fablabnk/SynthLabBadge/BuildGuide/ComponentImages/1.1k-ohm.png

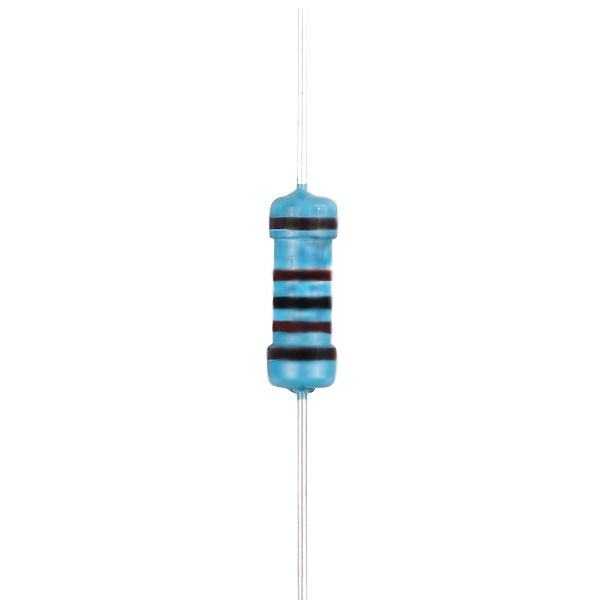
BuildGuide/ComponentImages/1.1k-ohm.png
