fablabnk/SynthLabBadge/BuildGuide/ComponentImages/1N4007.jpeg

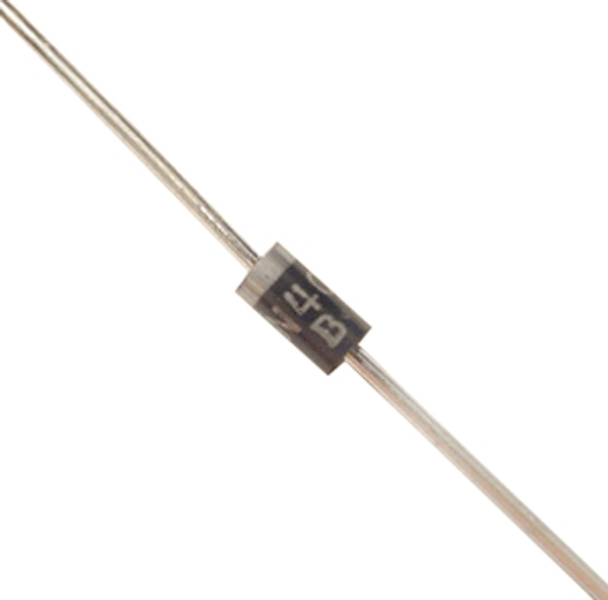
BuildGuide/ComponentImages/1N4007.jpeg
