fablabnk/SynthLabBadge/BuildGuide/ComponentImages/61201021621_sml.webp

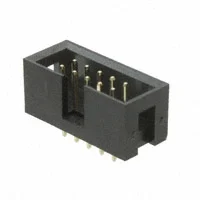
BuildGuide/ComponentImages/61201021621_sml.webp
