fablabnk/SynthLabBadge/BuildGuide/ComponentImages/download (1).jpeg

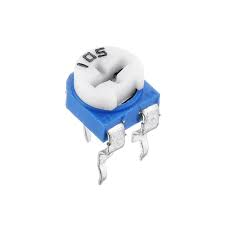
BuildGuide/ComponentImages/download (1).jpeg
