fablabnk/SynthLabBadge/BuildGuide/ComponentImages/download (2).jpeg

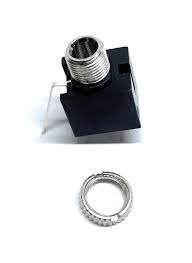
BuildGuide/ComponentImages/download (2).jpeg
