fablabnk/SynthLabBadge/BuildGuide/ComponentImages/download (3).jpeg

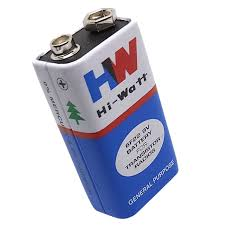
BuildGuide/ComponentImages/download (3).jpeg
