fablabnk/SynthLabBadge/BuildGuide/ComponentImages/images.jpeg

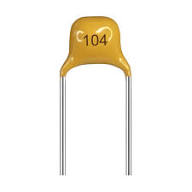
BuildGuide/ComponentImages/images.jpeg
