fablabnk/SynthLabBadge/BuildGuide/ComponentImages/shopping (1).webp

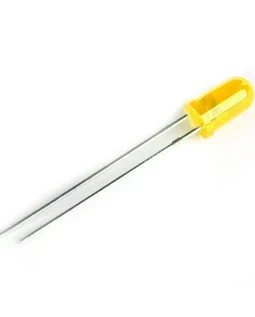
BuildGuide/ComponentImages/shopping (1).webp
