fablabnk/SynthLabBadge/BuildGuide/0-CompletedFront.png

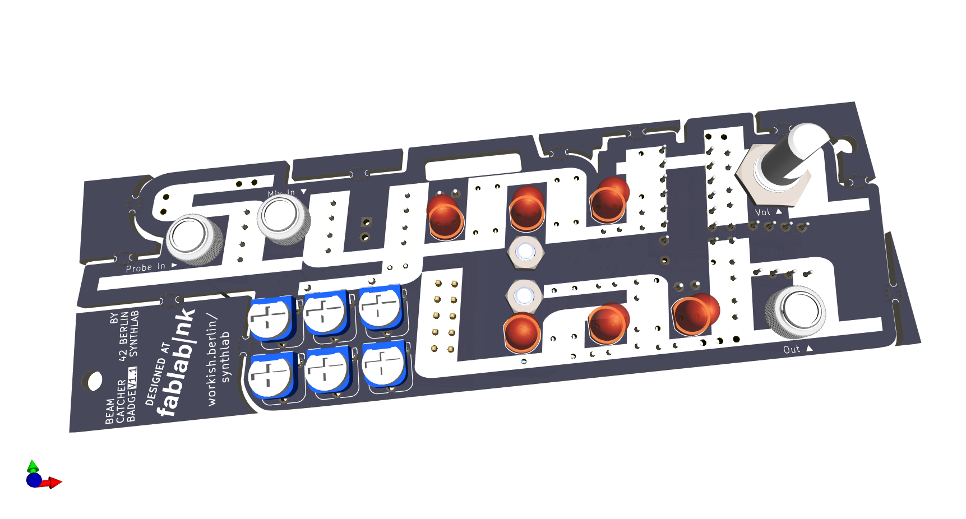
BuildGuide/0-CompletedFront.png
