fablabnk/SynthLabBadge/BuildGuide/0-FirstPage.png

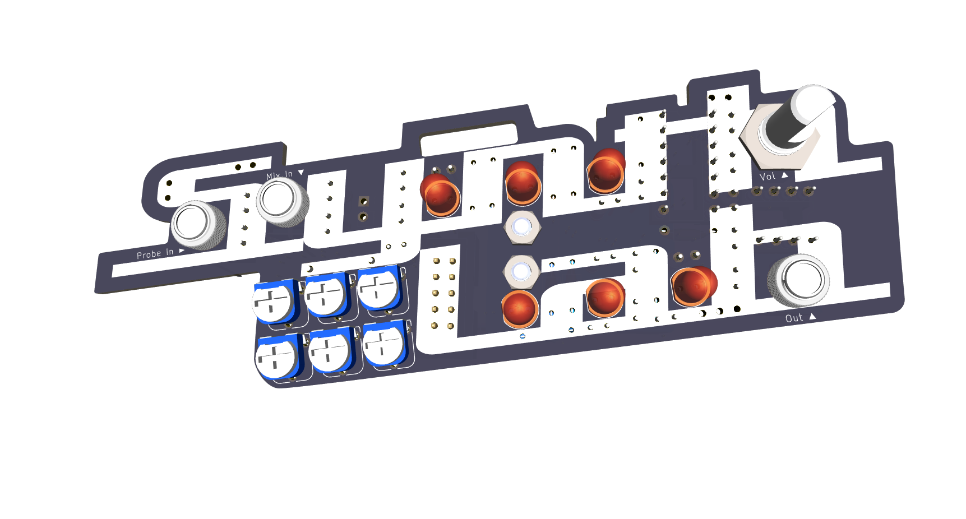
BuildGuide/0-FirstPage.png
