fablabnk/SynthLabBadge/BuildGuide/0-PCB.png

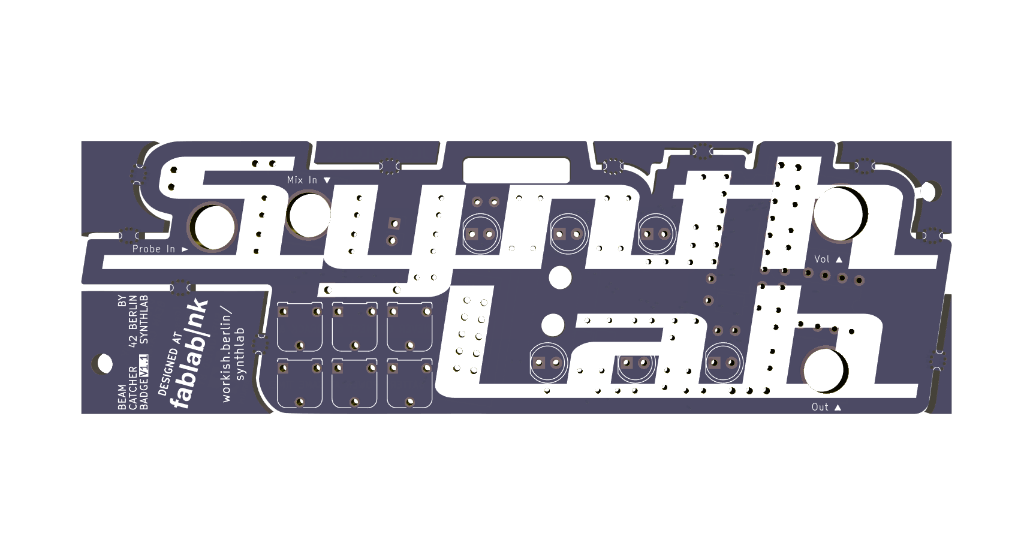
BuildGuide/0-PCB.png
