fablabnk/SynthLabBadge/BuildGuide/1-CompletedBack.png

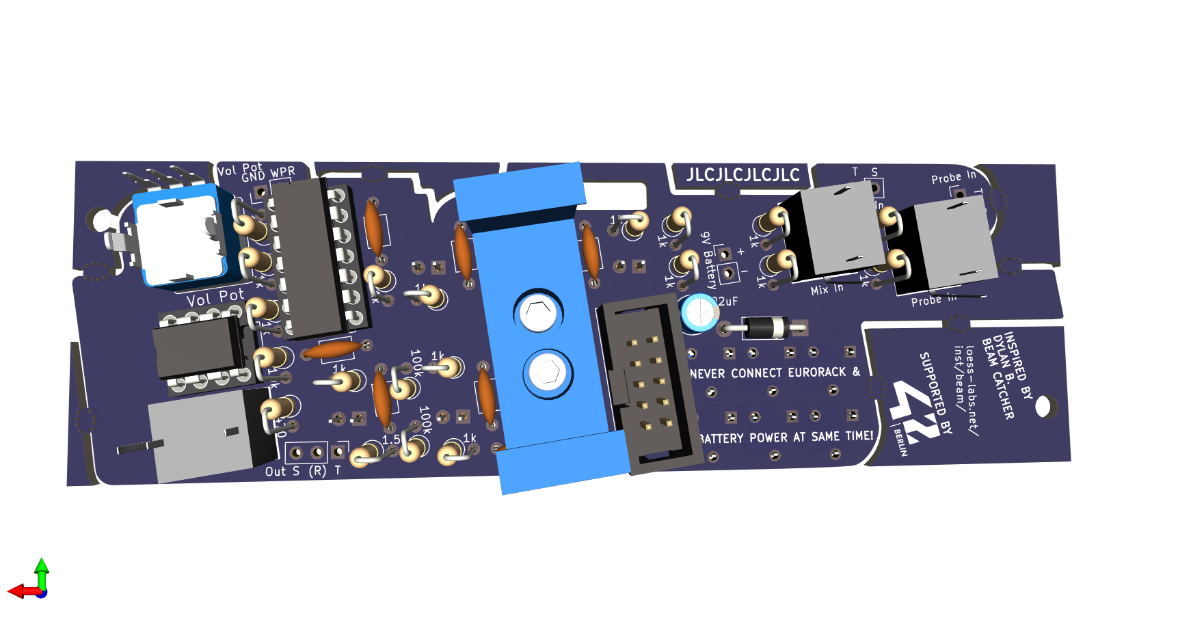
BuildGuide/1-CompletedBack.png
