fablabnk/SynthLabBadge/BuildGuide/2-CeramicCapsAndDiode.png

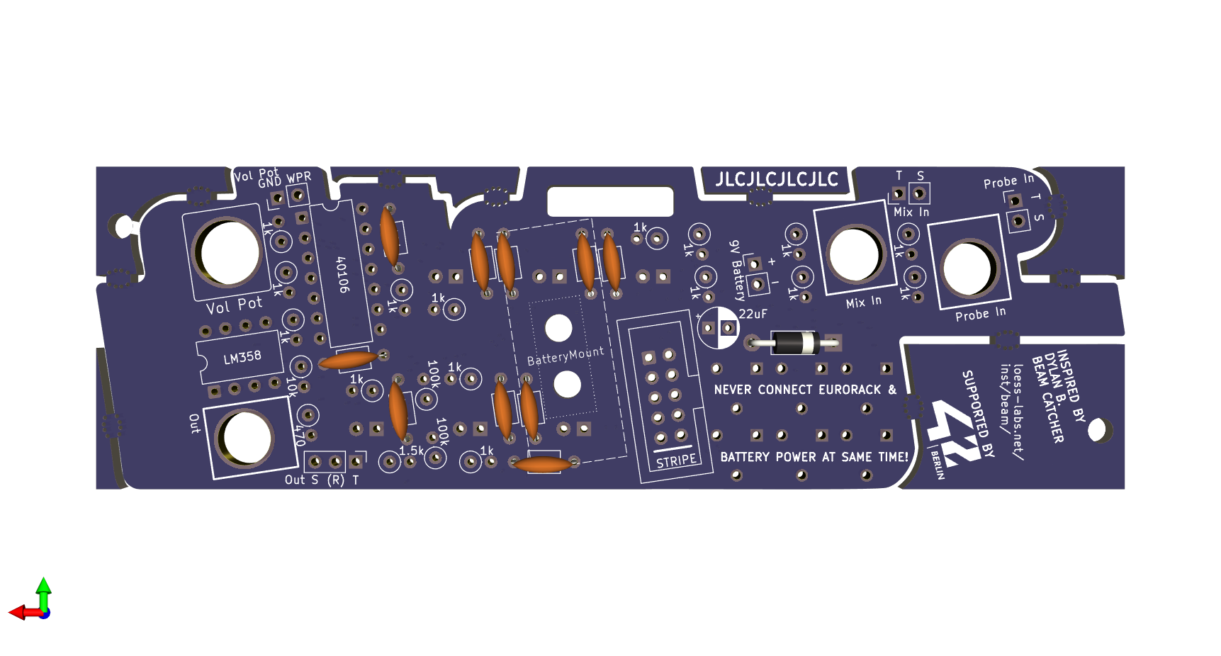
BuildGuide/2-CeramicCapsAndDiode.png
