fablabnk/SynthLabBadge/BuildGuide/4-LEDsTrimPots.png

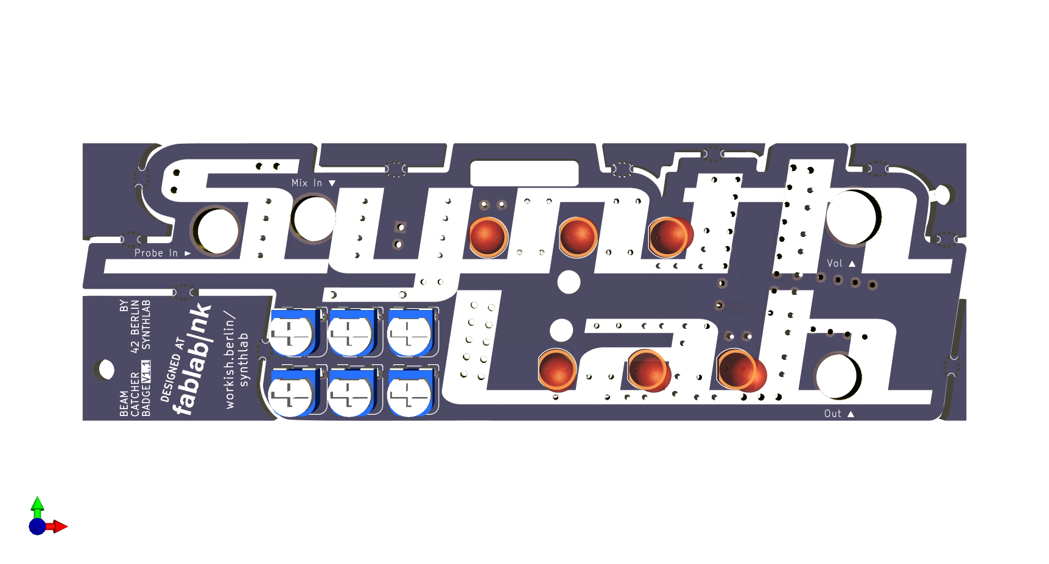
BuildGuide/4-LEDsTrimPots.png
