fablabnk/SynthLabBadge/BuildGuide/5-ICsIn.png

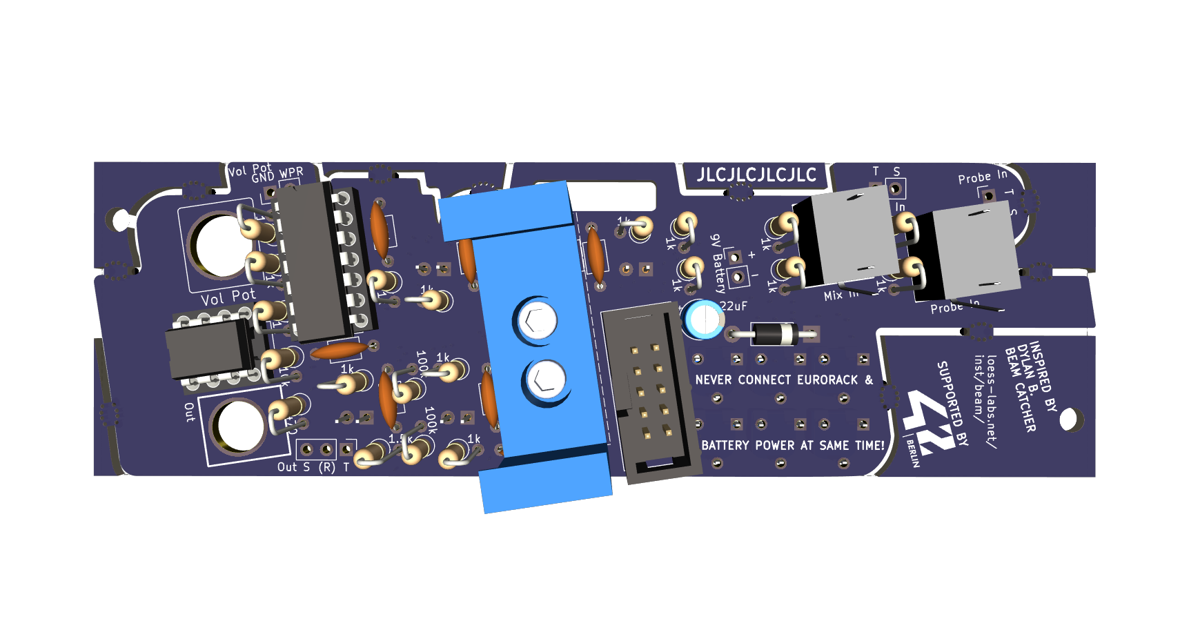
BuildGuide/5-ICsIn.png
