fablabnk/SynthLabBadge/BuildGuide/8-PtoP1.png

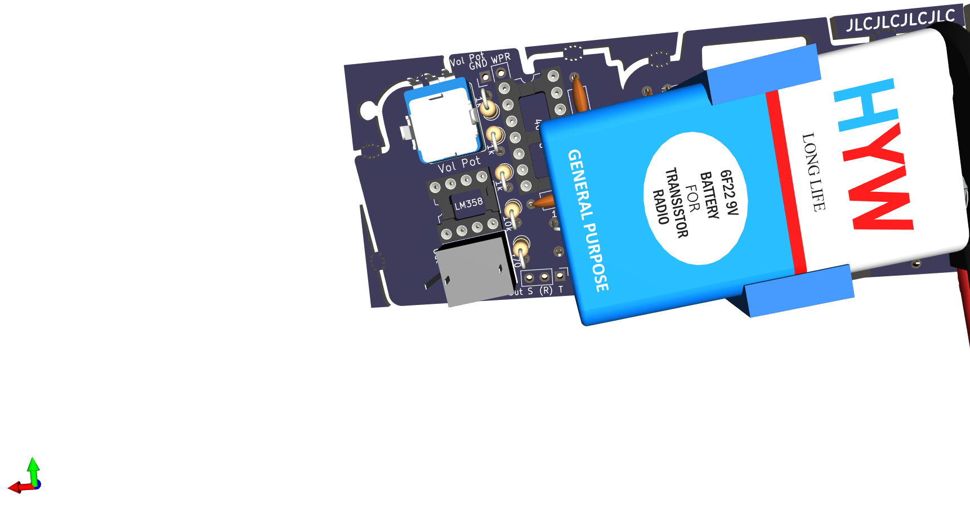
BuildGuide/8-PtoP1.png
