fablabnk/SynthLabBadge/BuildGuide/8-PtoP2.png

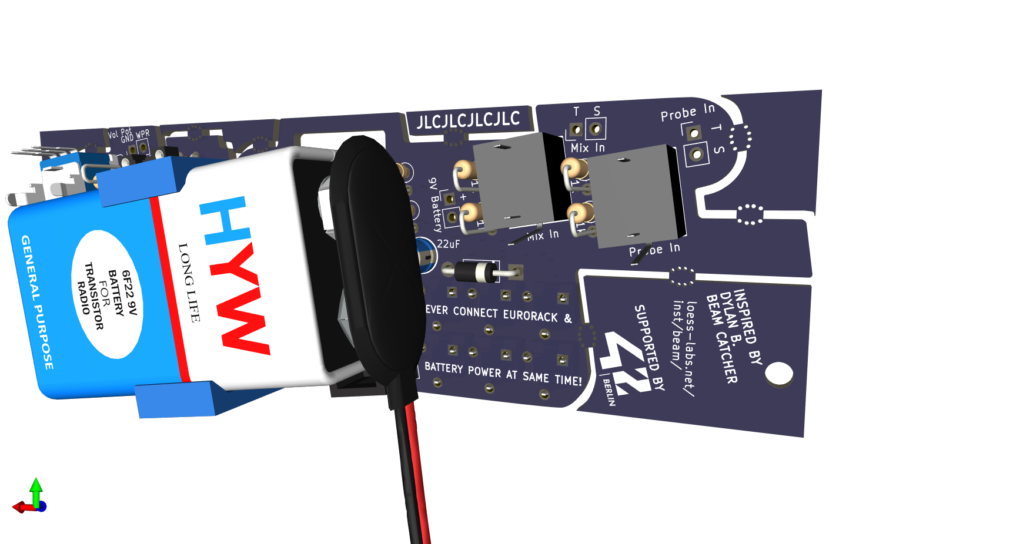
BuildGuide/8-PtoP2.png
