fablabnk/SynthLabBadge/BuildGuide/8-PtoP3.png

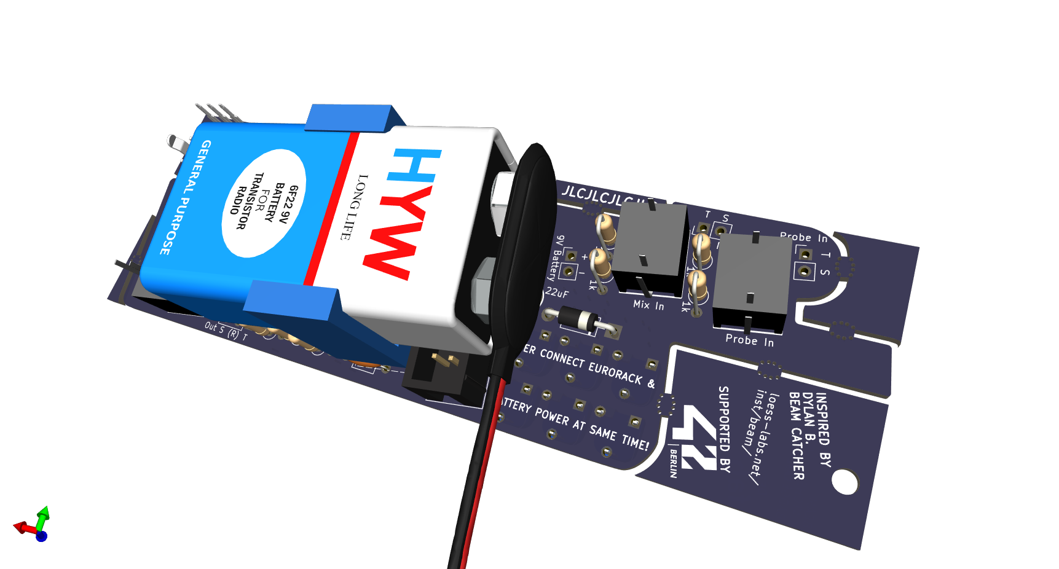
BuildGuide/8-PtoP3.png
