fablabnk/SynthLabBadge/BuildGuide/Probe.jpg

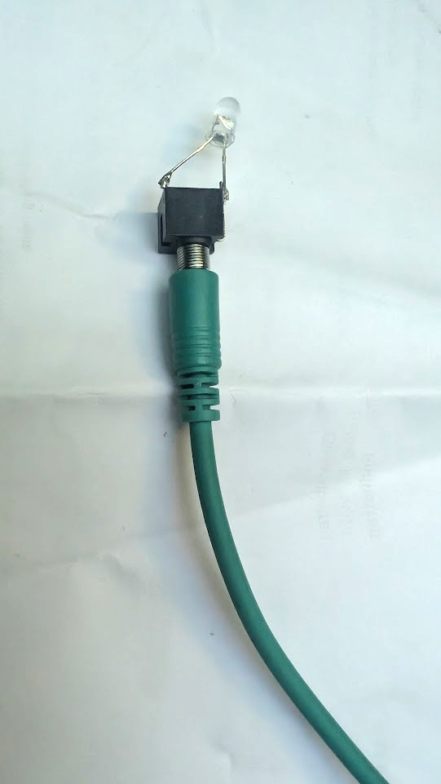
BuildGuide/Probe.jpg
