fablabnk/SynthLabBadge/BuildGuide/ProbeClose.jpg

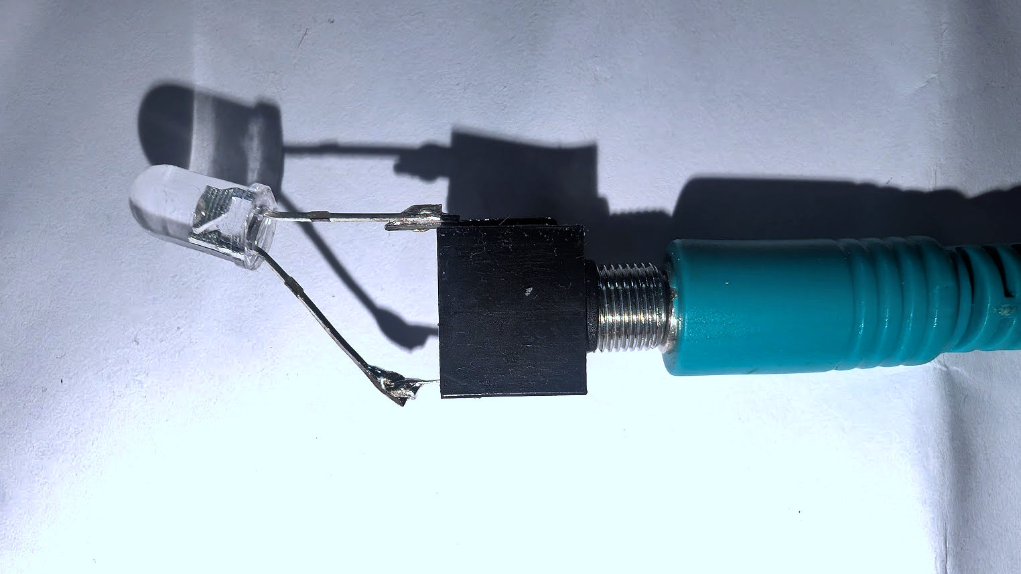
BuildGuide/ProbeClose.jpg
